zig-one/SnailPower/VA/battery/A/E-t.png

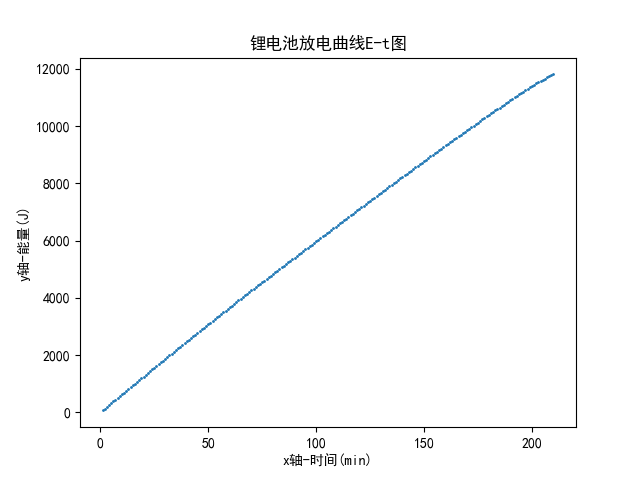
VA/battery/A/E-t.png
