zig-one/SnailPower/VA/battery/A/E-U.png

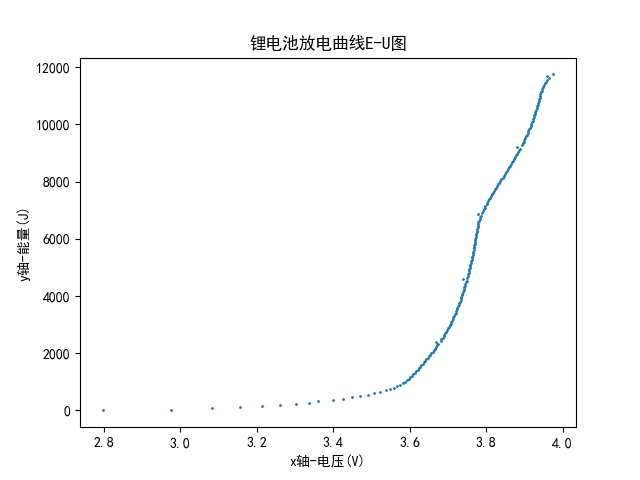
VA/battery/A/E-U.png
