zig-one/SnailPower/VA/battery/A/q_t.png

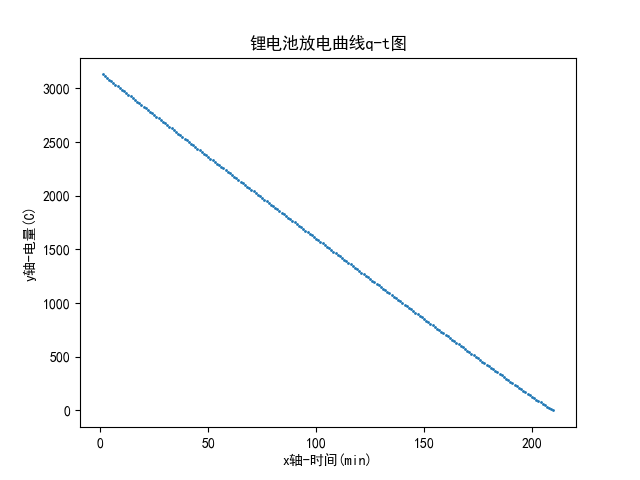
VA/battery/A/q_t.png
