zig-one/SnailPower/VA/battery/A/U_t.png

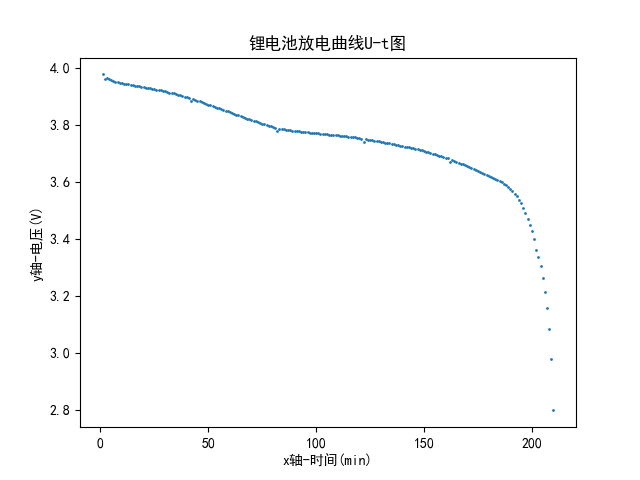
VA/battery/A/U_t.png
