zig-one/SnailPower/VA/sun/Figure_1.png

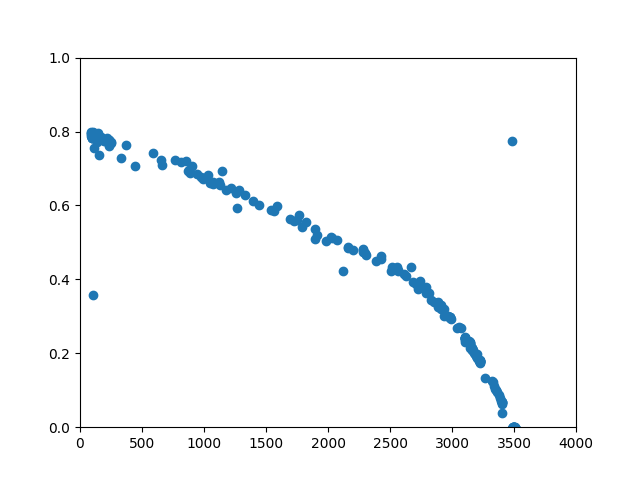
VA/sun/Figure_1.png
