zig-one/SnailPower/VA/battery/B/result/Ep-U.jpg

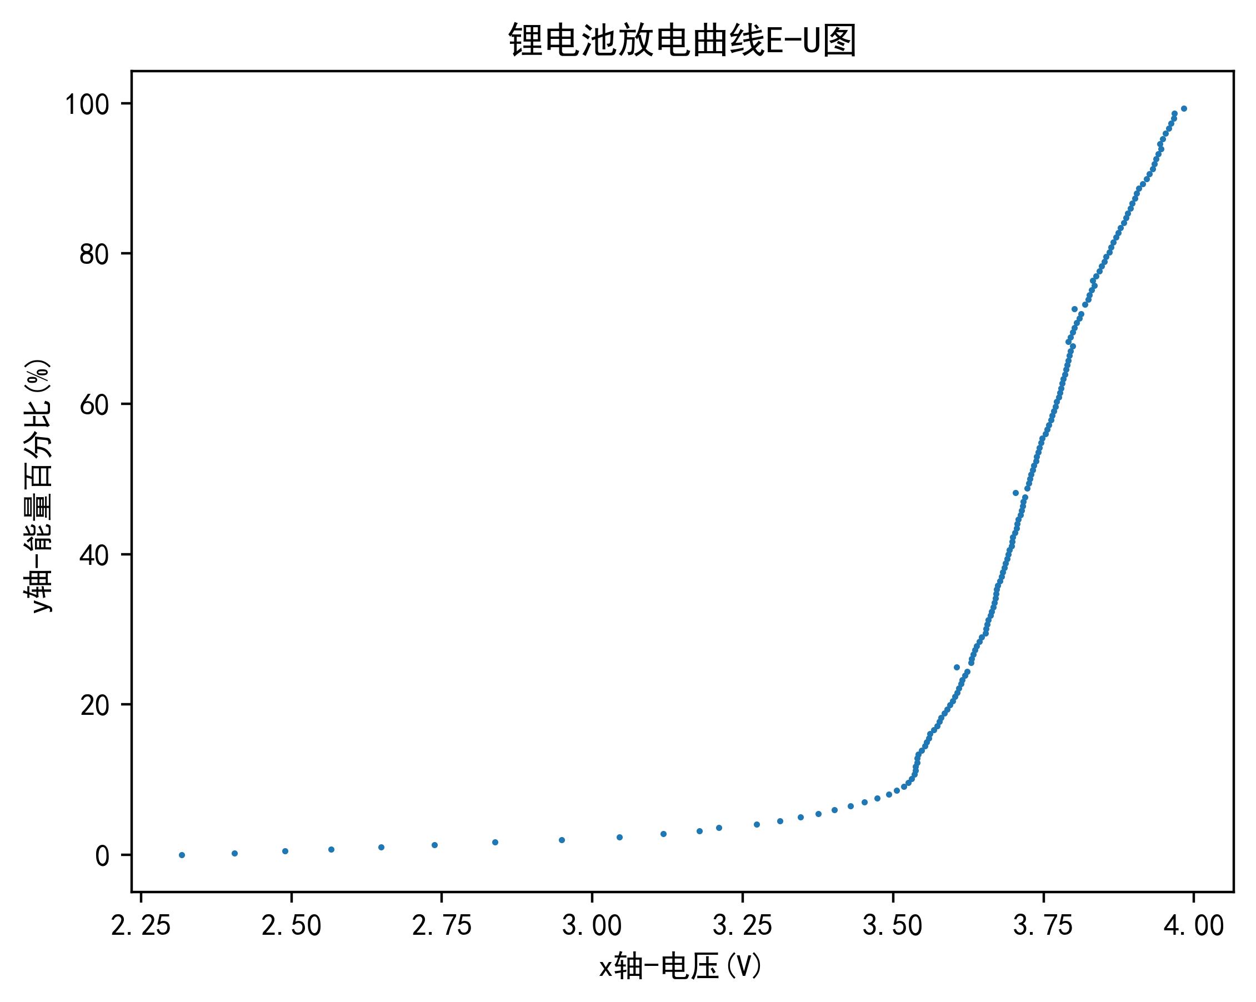
VA/battery/B/result/Ep-U.jpg
