zig-one/SnailPower/VA/battery/B/result/Et.jpg

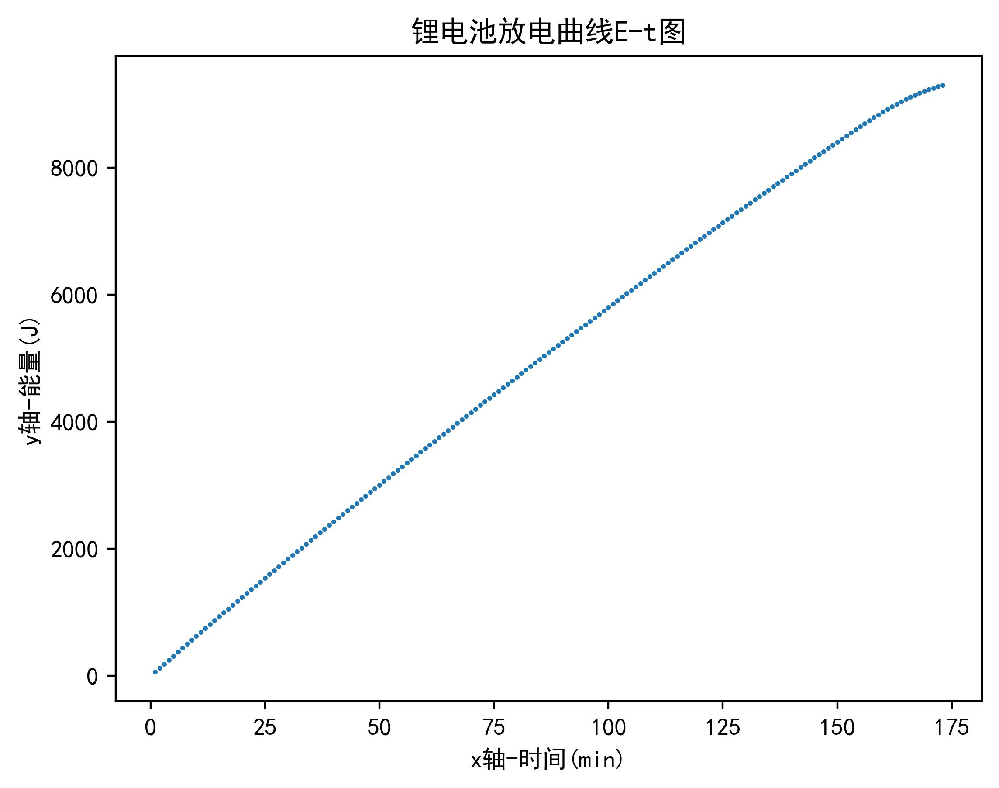
VA/battery/B/result/Et.jpg
