zig-one/SnailPower/VA/battery/B/result/EU.jpg

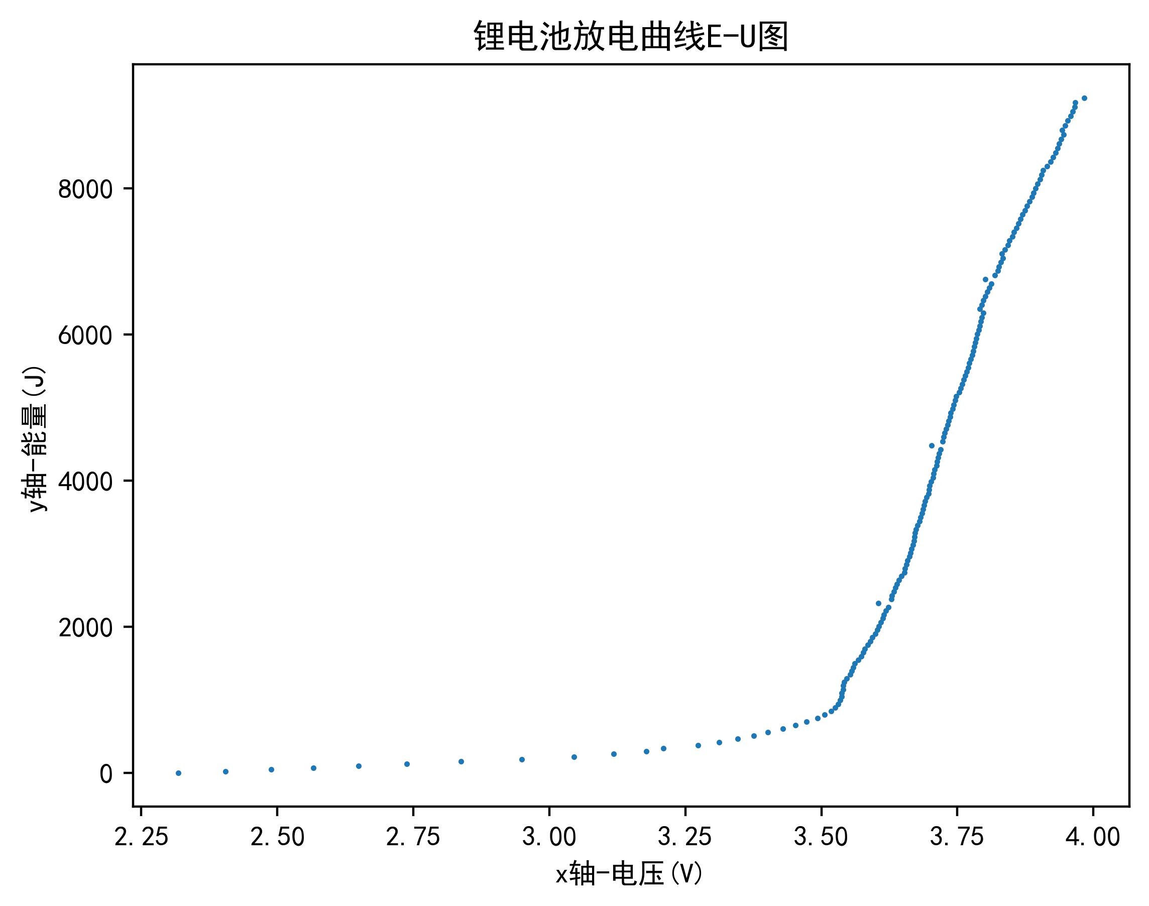
VA/battery/B/result/EU.jpg
