zig-one/SnailPower/VA/battery/B/result/qt.jpg

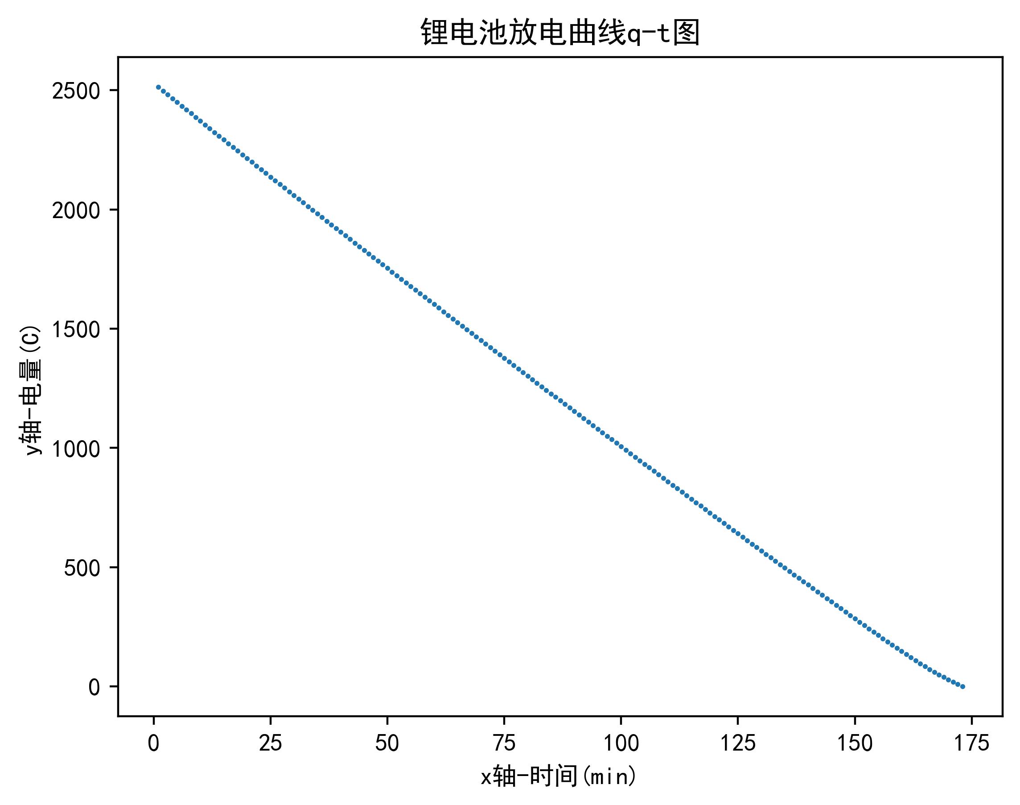
VA/battery/B/result/qt.jpg
