zig-one/SnailPower/VA/battery/B/result/Ut.jpg

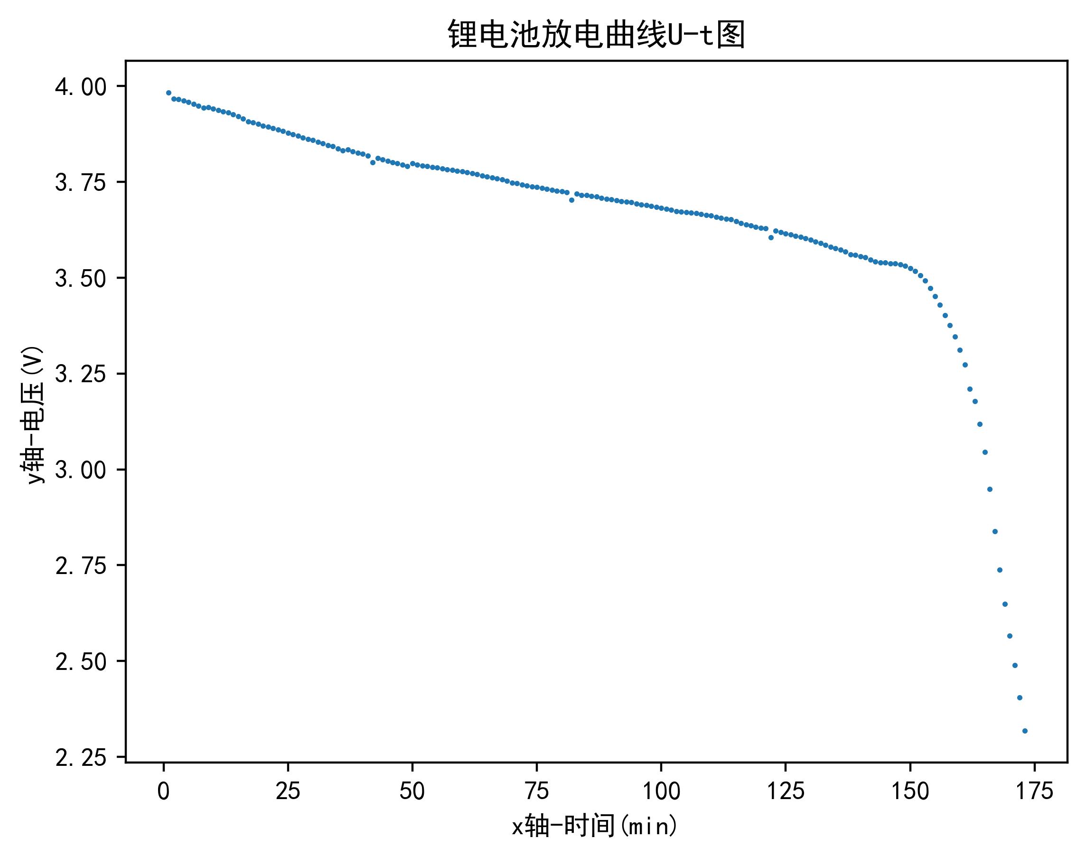
VA/battery/B/result/Ut.jpg
