zig-one/SnailPower/VA/battery/C/result/Ep-U.jpg

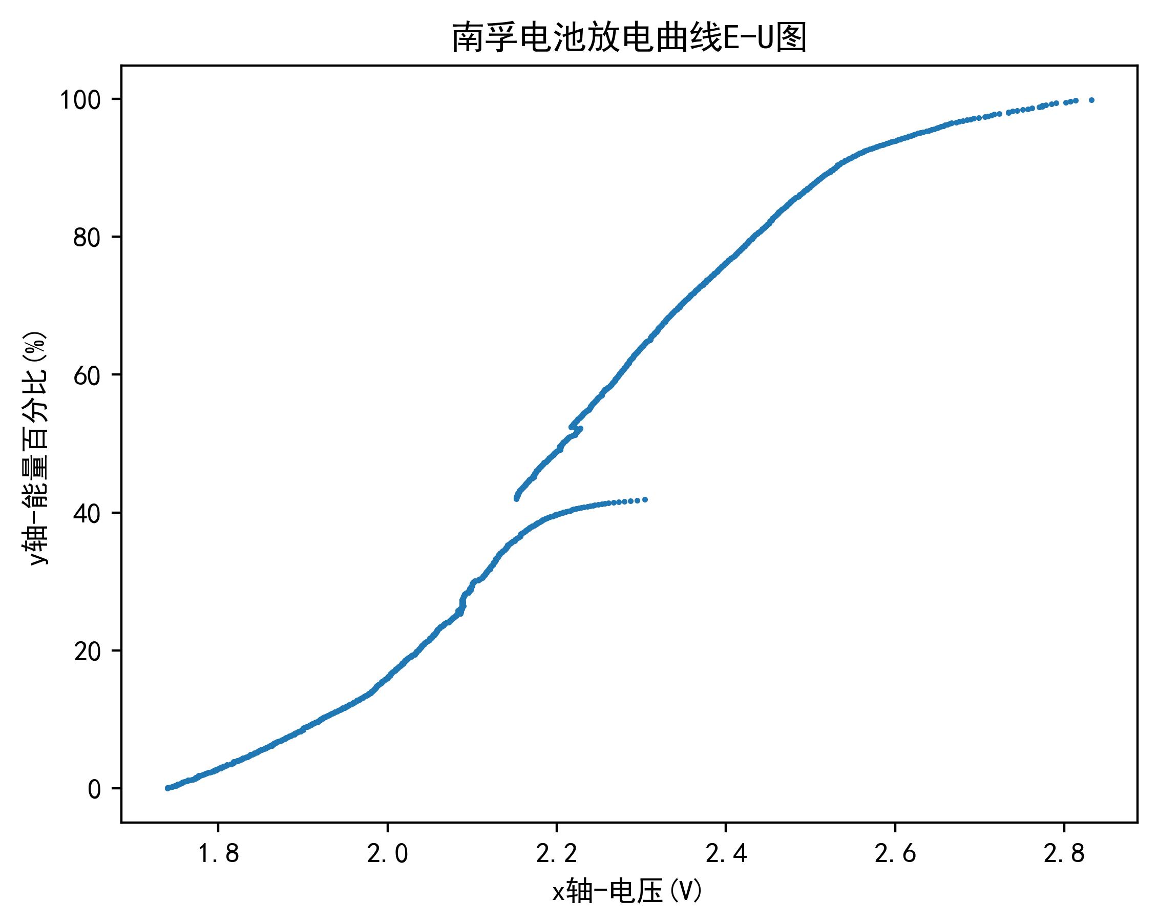
VA/battery/C/result/Ep-U.jpg
