zig-one/SnailPower/VA/battery/C/result/EU.jpg

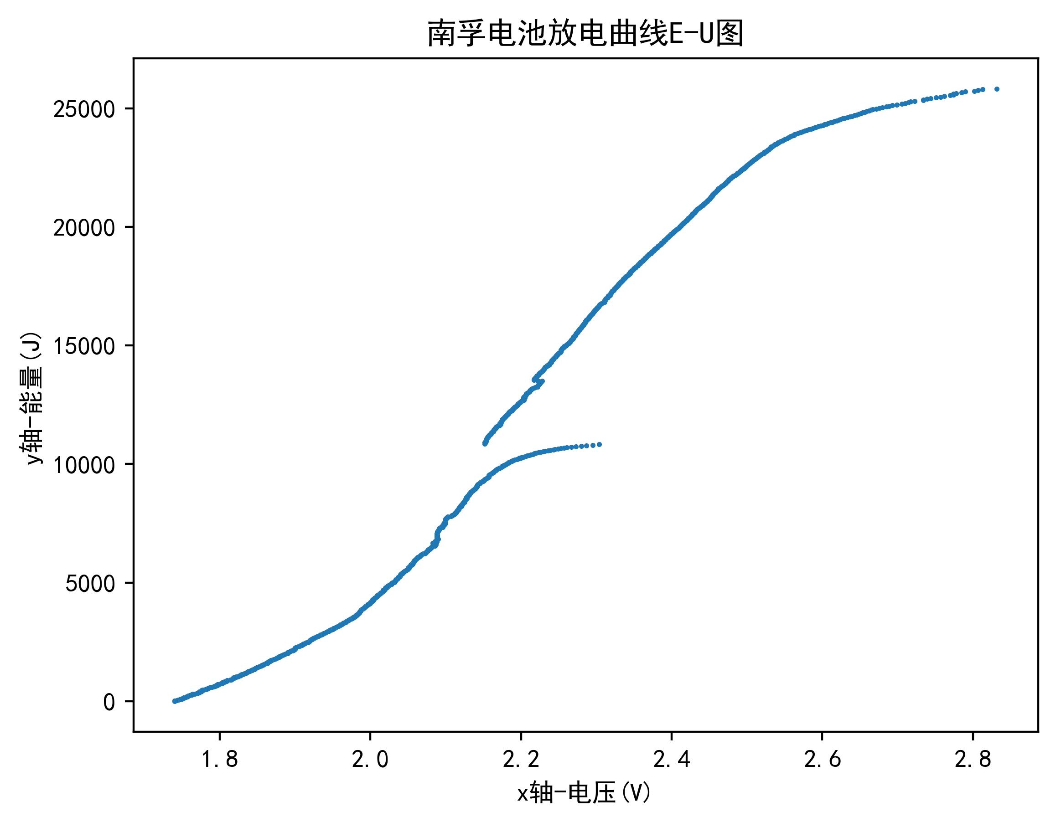
VA/battery/C/result/EU.jpg
