zig-one/SnailPower/VA/battery/C/result/Ut.jpg

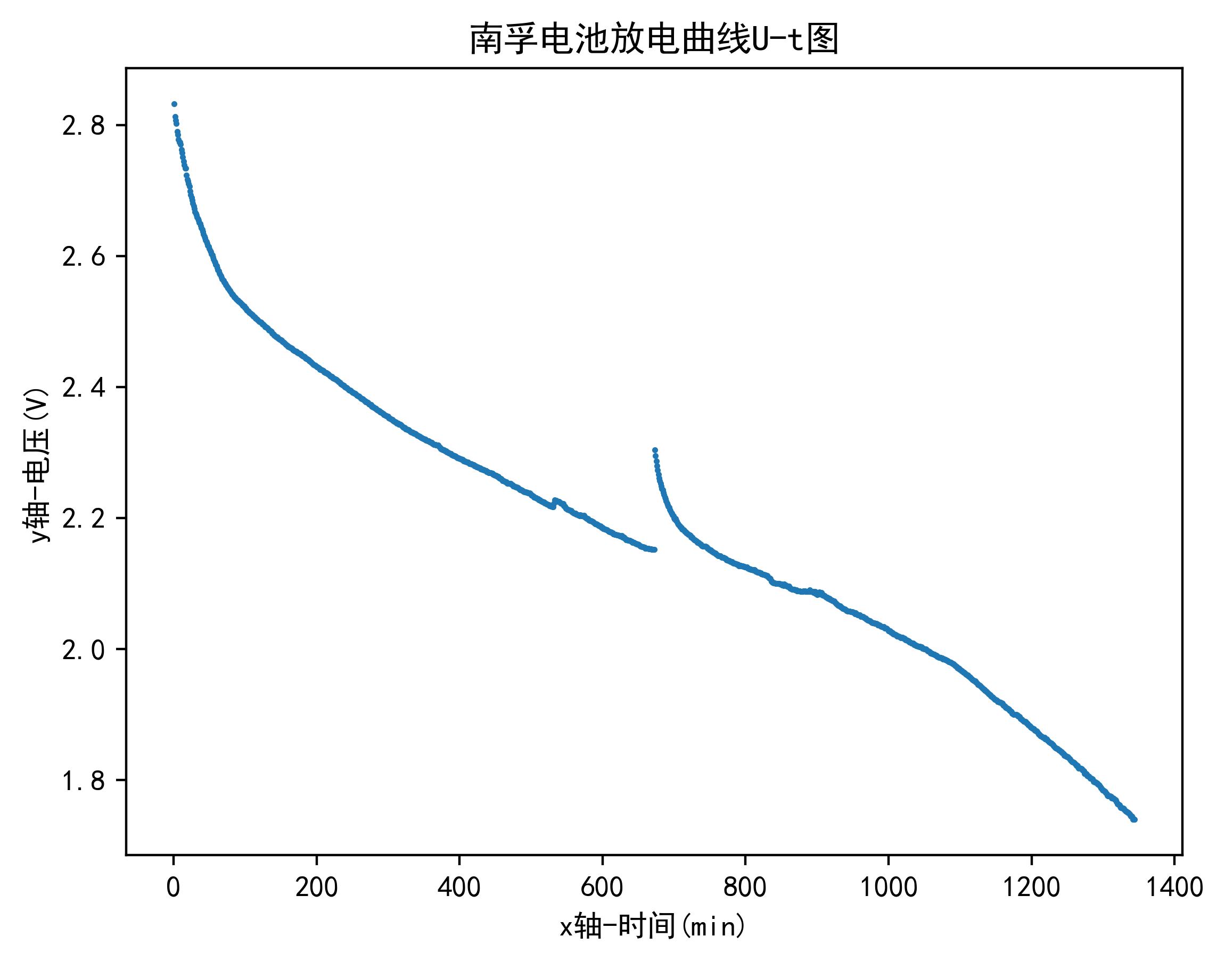
VA/battery/C/result/Ut.jpg
